gilbertfrancois/enviro-plus-case/photos/IMG_6688.jpg

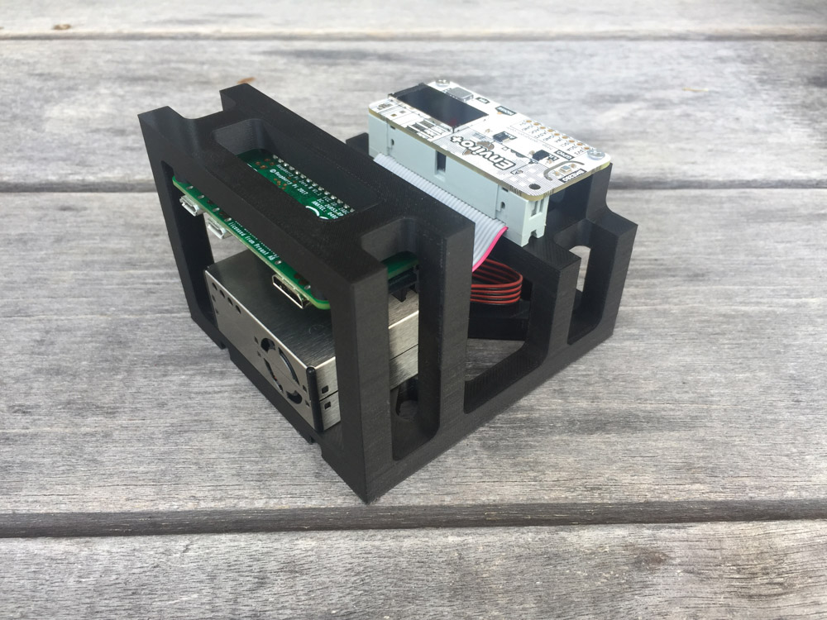
photos/IMG_6688.jpg
